wontaeyang/musubi/pictures/IMG_0832.jpg

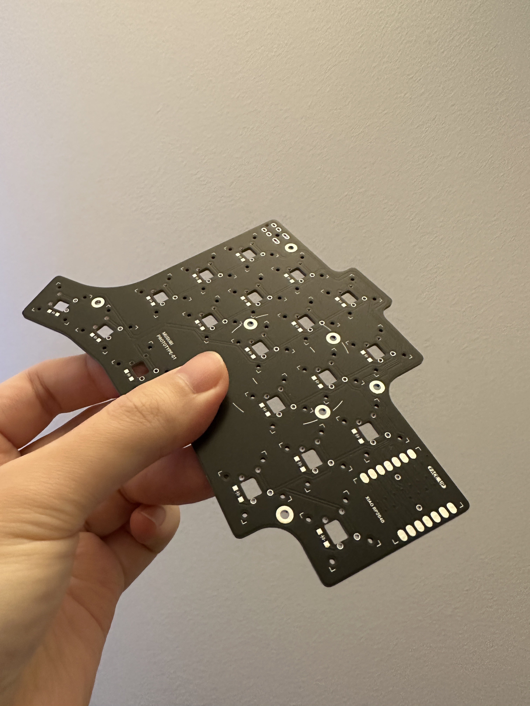
pictures/IMG_0832.jpg
